chevichelov/MEASURING_TWEEZER_YCHEV001/MEASURING_TWEEZER_YCHEV001/IMG.h

#pragma once
#include <Arduino.h>


//
static const unsigned char PROGMEM HEAD[] = { 0x0, 0x0, 0x0, 0x6, 0x0, 0x0, 0x0, 0x0, 0xc0, 0x0, 0xc0, 0x1, 0x81, 0x80, 0x20, 0x0, 0x0, 0x0, 0x8, 0x6, 0x0, 0x0, 0x0, 0x0, 0x87, 0x0, 0xc0, 0x0, 0x1, 0x80, 0x20, 0x0, 0x1a, 0x22, 0xde, 0xb7, 0xc, 0xc, 0x22, 0xd0, 0x98, 0x8c, 0xc1, 0x94, 0x19, 0x83, 0x22, 0x28, 0x1a, 0x72, 0xdc, 0xb7, 0x96, 0x1e, 0x73, 0xf8, 0x97, 0x5e, 0xf2, 0xd5, 0xad, 0xe5, 0xa7, 0x28, 0x1a, 0x52, 0xc8, 0xb6, 0x9e, 0x10, 0x5b, 0xf9, 0x29, 0x50, 0xf3, 0xd4, 0xbd, 0xe7, 0xa5, 0x28, 0x1a, 0xd2, 0xc8, 0xb6, 0xd0, 0x10, 0xda, 0xd9, 0x29, 0x50, 0xd2, 0x14, 0xa1, 0xa4, 0x2d, 0x28, 0x1e, 0xf3, 0xcc, 0xf7, 0x92, 0x10, 0xf2, 0xd9, 0x17, 0x90, 0xd2, 0x5c, 0xa5, 0xa4, 0xaf, 0x38, 0x1e, 0x73, 0xcc, 0xf7, 0x9e, 0xde, 0x72, 0xdb, 0x18, 0x1e, 0xd3, 0xdc, 0xbd, 0xa7, 0xa7, 0x38, 0x2, 0x63, 0x4c, 0xd3, 0xc, 0xcc, 0x62, 0xda, 0x7, 0xc, 0xd1, 0x88, 0x99, 0xa3, 0x26, 0x10, 0x1e, 0x0, 0x0, 0x0, 0x0, 0x0, 0x0, 0x2, 0x0, 0x0, 0x0, 0x0, 0x0, 0x0, 0x0, 0x0, 0x1c, 0x0, 0x0, 0x0, 0x0, 0x0, 0x0, 0x4, 0x0, 0x0, 0x0, 0x0, 0x0, 0x0, 0x0, 0x0 };
//
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
